MangoIV/cheap_boi/pictures/pcb_front_closeup.jpeg

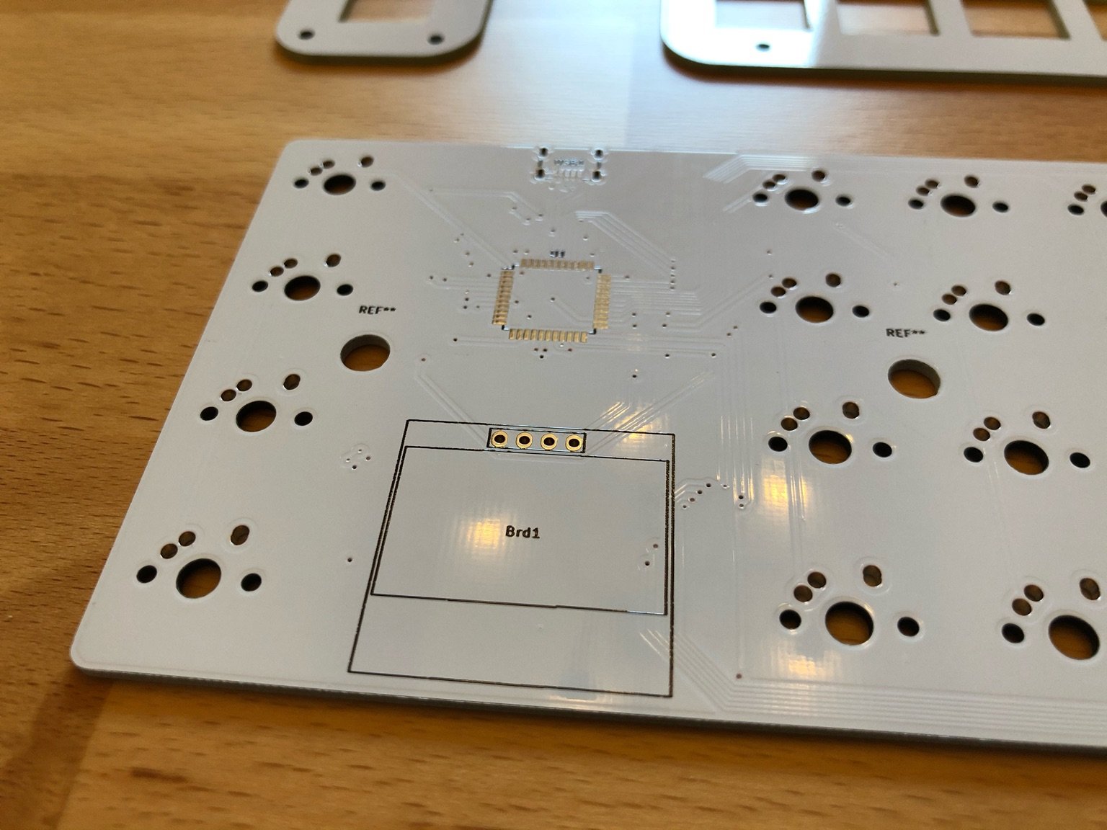
pictures/pcb_front_closeup.jpeg
