MangoIV/cheap_boi/pictures/plate_back_closeup.jpeg

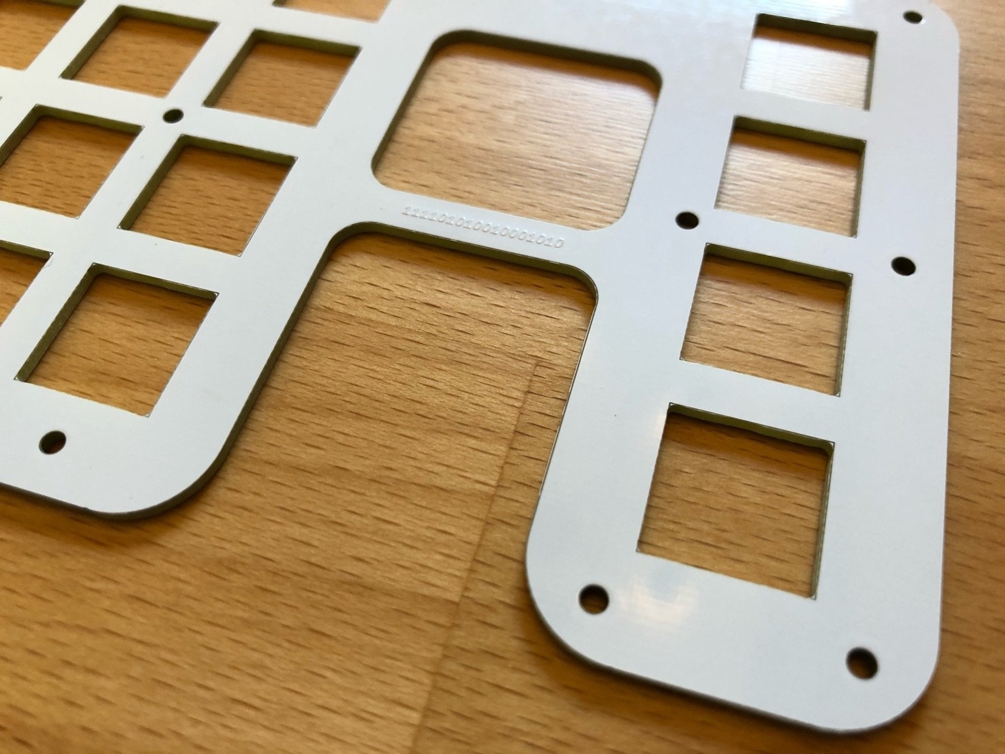
pictures/plate_back_closeup.jpeg
